JGAguado/Smart_Alarm/Documentation/Silkscreen/Bottom.bmp

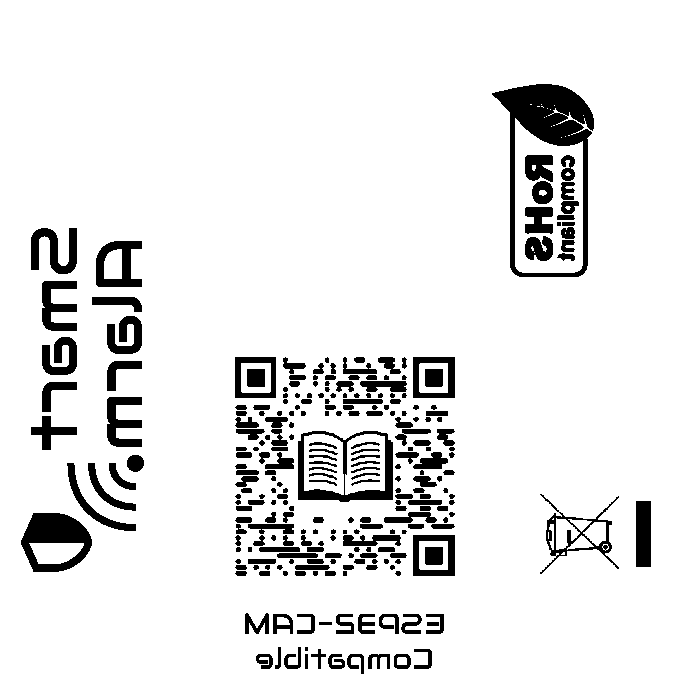
Documentation/Silkscreen/Bottom.bmp
