JGAguado/Smart_Alarm/Documentation/Silkscreen/Top.bmp

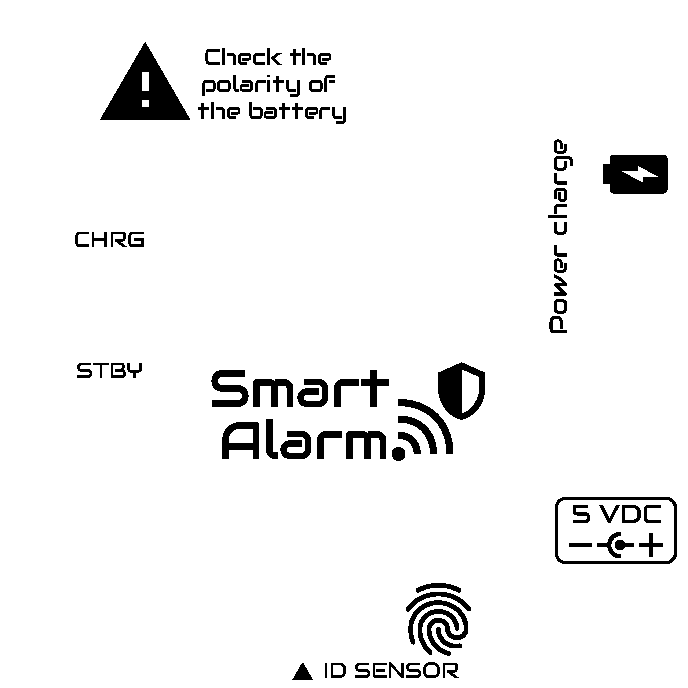
Documentation/Silkscreen/Top.bmp
